AOD-gm/Timer_Counter-STM32F103C8T6-/Core/Inc/Menu_UI.h

#ifndef Menu_UI_H
#define Menu_UI_H
#include "main.h"
#include <stdint.h>
#include "SSD1306.h"
#include "MH-R38.h"
#include "DS3231.h"
#include "HLK_LD2410.h"
#include <stdio.h> 
#include <string.h>
#include "Esp_01.h"
extern uint8_t u8_RxBuff[50];
extern uint8_t RxIndex;
extern uint8_t Rx_Flag;
extern uint8_t alarm_set;
extern uint8_t temp_alarm_h, temp_alarm_m, temp_alarm_s;

void UI_ESP_Process(void);
void UI_System_Process(void);
void UI_Proccess_Keypad(char key);
void UI_Proccess_IR(uint32_t IR_Code);
void UI_Render(void);
#endif
